janek-2115/Marshall-Stanmore-Schematic/audio.kicad_sch

## KiCad design audio.kicad_sch (2026-05-27)

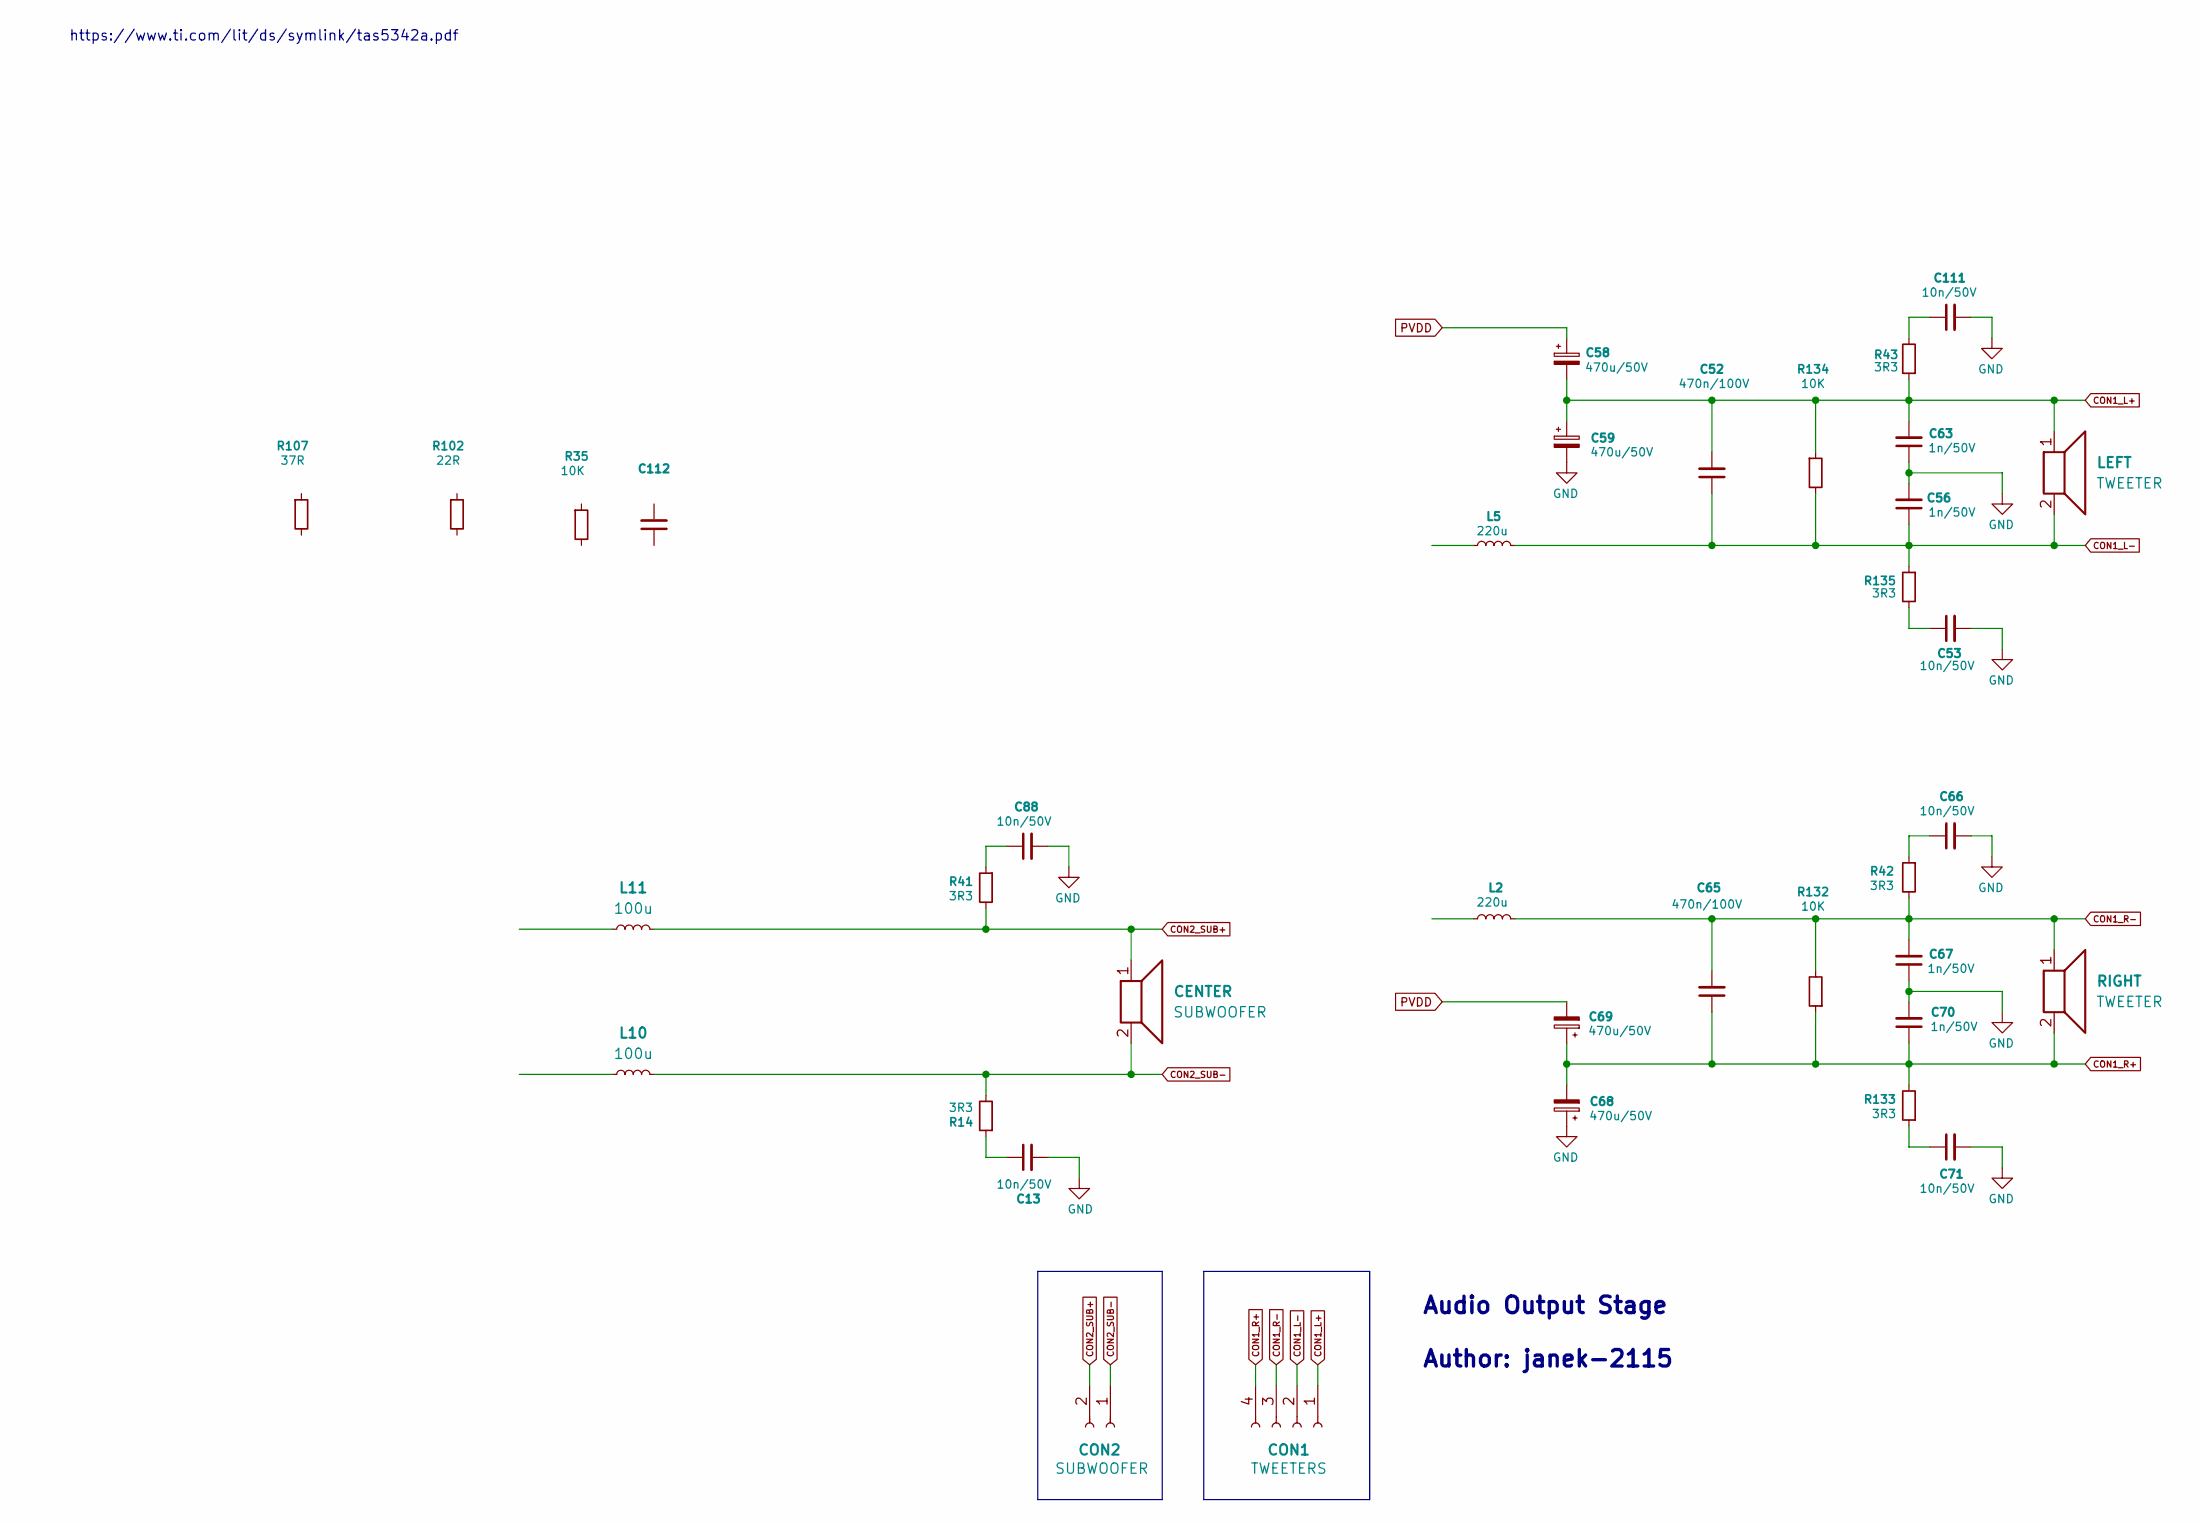
[picture p4: schematic audio.kicad_sch]

Parts:
C13, C53, C66, C71, C88, C111: 10n/50V
C52, C65: 470n/100V
C56, C63, C67, C70: 1n/50V
C58, C59, C68, C69: 470u/50V
C112: (no value)
CENTER: SUBWOOFER
CON1: TWEETERS
CON2: SUBWOOFER
L2, L5: 220u
L10, L11: 100u
LEFT: TWEETER
R14, R41, R42, R43, R133, R135: 3R3
R35, R132, R134: 10K
R102: 22R
R107: 37R
RIGHT: TWEETER

Connections:
CON1_L+: C52.2, C58.2, C59.1, C63.2, CON1.1, LEFT.1, R43.1, R134.1
CON1_L-: C52.1, C56.1, CON1.2, L5.2, LEFT.2, R134.2, R135.1
CON1_R+: C65.1, C68.2, C69.1, C70.1, CON1.4, R132.1, R133.2, RIGHT.2
CON1_R-: C65.2, C67.2, CON1.3, L2.2, R42.2, R132.2, RIGHT.1
CON2_SUB+: CENTER.1, CON2.2, L11.2, R41.2
CON2_SUB-: CENTER.2, CON2.1, L10.2, R14.2
GND: C13.2, C53.2, C56.2, C59.2, C63.1, C66.2, C67.1, C68.1, C70.2, C71.2, C88.2, C111.2
unnamed: C13.1, R14.1
unnamed: C53.1, R135.2
unnamed: C66.1, R42.1
unnamed: C71.1, R133.1
unnamed: C88.1, R41.1
unnamed: C111.1, R43.2
PVDD: C58.1, C69.2

Notes on the sheet:
Audio Output Stage Author: janek-2115
https://www.ti.com/lit/ds/symlink/tas5342a.pdf
