janek-2115/Marshall-Stanmore-Schematic/power.kicad_sch

## KiCad design power.kicad_sch (2026-05-27)

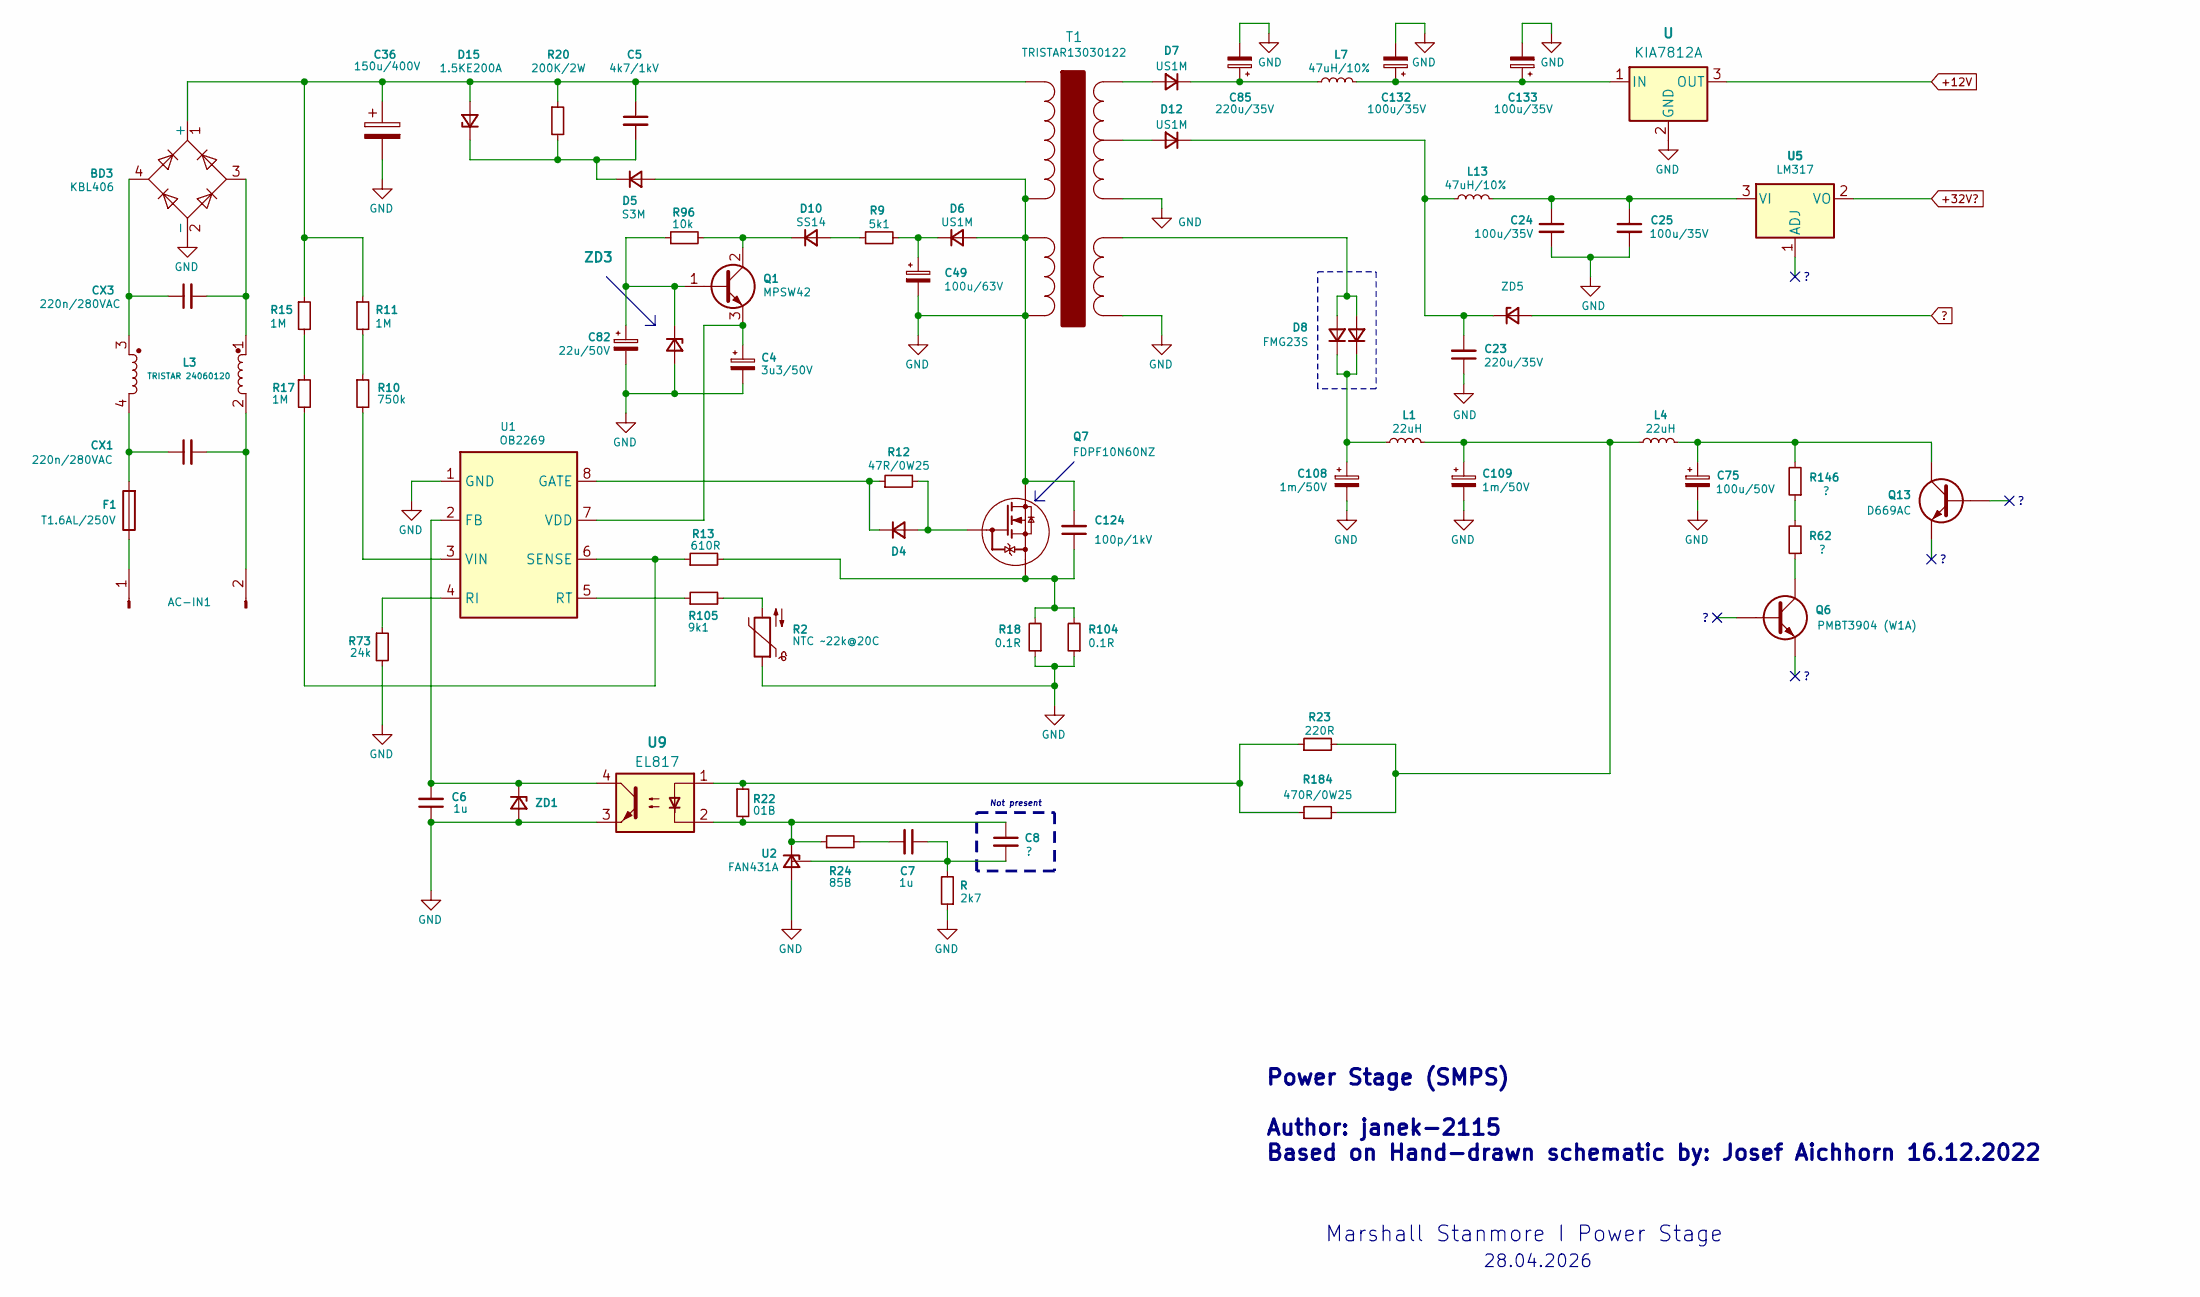
[picture p5: schematic power.kicad_sch]

Parts:
AC-IN1: AC-IN1
BD3: KBL406; Diode_Bridge_Diotec_ABS
C4: 3u3/50V
C5: 4k7/1kV
C6, C7: 1u
C8: ?
C23, C85: 220u/35V
C24, C25, C132, C133: 100u/35V
C36: 150u/400V
C49: 100u/63V
C75: 100u/50V
C82: 22u/50V
C108, C109: 1m/50V
C124: 100p/1kV
CX1, CX3: 220n/280VAC
D4: (no value)
D5: S3M
D6, D7, D8, D12: US1M
D10: SS14
D15: 1.5KE200A; D_DO-201AE_P15.24mm_Horizontal
F1: T1.6AL/250V
L1, L4: 22uH
L3: TRISTAR 24060120
L7, L13: 47uH/10%
Q1: MPSW42; TO-92
Q6: PMBT3904 (W1A)
Q7: FDPF10N60NZ; TO-220F-3_Vertical
Q13: D669AC
R: 2k7
R2: NTC ~22k@20C
R9: 5k1
R10: 750k
R11, R15, R17: 1M
R12: 47R/0W25
R13: 610R
R18, R104: 0.1R
R20: 200K/2W
R22: 01B
R23: 220R
R24: 85B
R62, R146: ?
R73: 24k
R96: 10k
R105: 9k1
R184: 470R/0W25
T1: TRISTAR13030122
U: KIA7812A
U1: OB2269; SOIC-8_3.9x4.9mm_P1.27mm
U2: FAN431A; TO-92
U5: LM317; TO-220-3_Vertical
U9: EL817
ZD1, ZD3, ZD5: (no value)

Connections:
+12V: U.3 (OUT)
+32V?: U5.2 (VO)
?: ZD5.2 (A)
GND: BD3.2 (-), C4.2, C6.1, C23.1, C24.2, C25.2, C36.2, C49.2, C75.2, C82.2, C85.2, C108.2, C109.2, C124.2, C132.2, C133.2, D5.2 (A), D6.2 (A), Q7.D, R.1, R2.1, R18.1, R73.2, R104.1, T1.5, T1.6, U.2 (GND), U1.1 (GND), U2.2 (ANODE), U9.3, ZD1.2 (A), ZD3.2 (A)
unnamed: AC-IN1.1, F1.1
unnamed: AC-IN1.2, CX1.2, L3.2
unnamed: BD3.1 (+), C5.1, C36.1, D15.2 (A), R11.1, R15.1, R20.1, T1.5
unnamed: BD3.3, CX3.2, L3.1
unnamed: BD3.4, CX3.1, L3.3
unnamed: C4.1, Q1.3 (E), U1.7 (VDD)
unnamed: C5.2, D5.1 (K), D15.1 (K), R20.2
unnamed: C6.2, U1.2 (FB), U9.4, ZD1.1 (K)
unnamed: C7.1, C8.2, R.2, U2.3 (CATHODE)
unnamed: C7.2, R24.2
unnamed: C8.1, R22.2, R24.1, U2.3 (CATHODE), U9.2
unnamed: C23.2, D12.1 (K), L13.1, ZD5.1 (K)
unnamed: C24.1, C25.1, L13.2, U5.3 (VI)
unnamed: C49.1, D6.1 (K), R9.2
unnamed: C75.1, L4.2, Q13.C, R146.2
unnamed: C82.1, Q1.1 (B), R96.1, ZD3.1 (K)
unnamed: C85.1, D7.1 (K), L7.1
unnamed: C108.1, D8.1 (K), L1.1
unnamed: C109.1, L1.2, L4.1, R23.2, R184.2
unnamed: C124.1, Q7.S, R13.2, R18.2, R104.2
unnamed: C132.1, C133.1, L7.2, U.1 (IN)
unnamed: CX1.1, F1.2, L3.4
unnamed: D4.1 (K), R12.1, U1.8 (GATE)
unnamed: D4.2 (A), Q7.G, R12.2
unnamed: D7.2 (A), T1.6
unnamed: D8.2 (A), T1.6
unnamed: D10.1 (K), Q1.2 (C), R96.2
unnamed: D10.2 (A), R9.1
unnamed: D12.2 (A), T1.6
unnamed: Q6.C, R62.1
unnamed: R10.1, R11.2
unnamed: R10.2, U1.3 (VIN)
unnamed: R13.1, R17.2, U1.6 (SENSE)
unnamed: R15.2, R17.1
unnamed: R73.1, U1.4 (RI)
unnamed: R105.1, U1.5 (RT)
unnamed: R2.2, R105.2
unnamed: R62.2, R146.1
unnamed: R22.1, R23.1, R184.1, U9.1

Notes on the sheet:
Power Stage (SMPS) Author: janek-2115 Based on Hand-drawn schematic by: Josef Aichhorn 16.12.2022
Not present
Marshall Stanmore I Power Stage
28.04.2026
